llextv/coreLight/Images/image-10.png

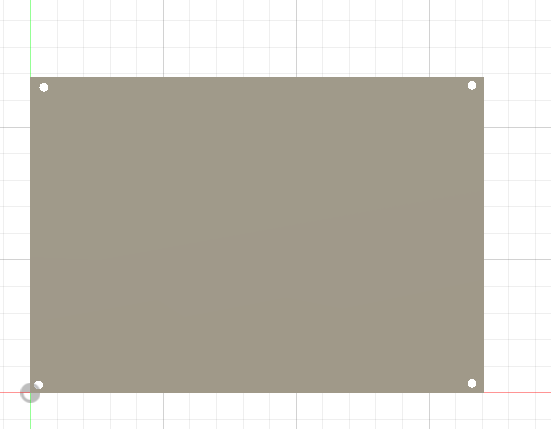
Images/image-10.png
