llextv/coreLight/Images/image-42.png

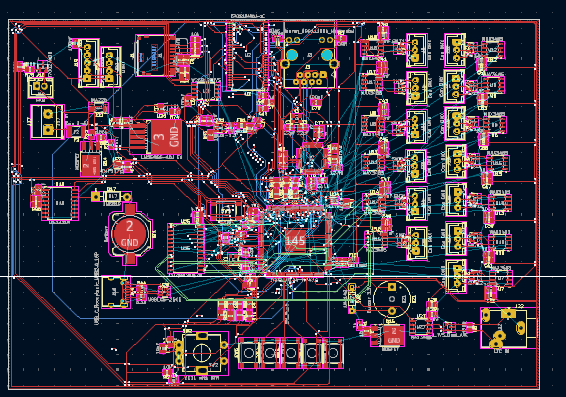
Images/image-42.png
