llextv/coreLight/Images/image-43.png

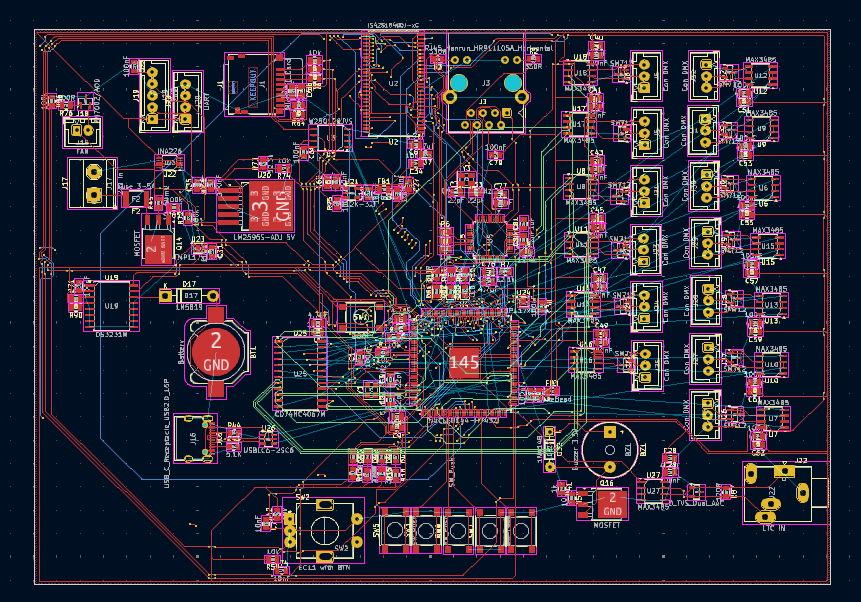
Images/image-43.png
